esitarski/LaserJig/lasercut/lasercut.scad

UP = 0;
DOWN = 180;
LEFT = 90;
RIGHT = 270;
MID = 360;
kerf=0.0;// Hacky global for kerf

generate = 0; 

if (generate == 1)
{
    // openscad examples.scad -D generate=1 -o /tmp/d.csg 2>&1 >/dev/null  | sed 's/ECHO: \"\[LC\] //' | sed 's/"$//' | sed '$a;' >./generate.scad ; openscad ./generate.scad -o generate.dxf
    // (from http://forum.openscad.org/Sharing-Dump-echo-output-to-a-file-td12529.html)
//    echo("[LC] use <lasercut.scad>; \nprojection(cut = false) \n\t");
}


module lasercutoutSquare(thickness, x=0, y=0, 
        simple_tabs=[], simple_tab_holes=[], 
        captive_nuts=[], captive_nut_holes = [],
        finger_joints = [],
        bumpy_finger_joints = [],
        screw_tabs=[], screw_tab_holes=[],
        twist_holes=[], twist_connect=[],
        clips=[], clip_holes=[],
        circles_add = [],
        circles_remove = [],
        slits = [],
        cutouts = [],
        cutouts_vb = [],
        flat_adjust = [],
        milling_bit = 0.0,
)
{
    points = [[0,0], [x,0], [x,y], [0,y], [0,0]];
lasercutout(thickness=thickness,  
        points = points, 
        simple_tabs = simple_tabs, 
        simple_tab_holes = simple_tab_holes, 
        captive_nuts = captive_nuts, 
        captive_nut_holes = captive_nut_holes,
        finger_joints = finger_joints,
        bumpy_finger_joints = bumpy_finger_joints,
        screw_tabs= screw_tabs, screw_tab_holes= screw_tab_holes,
        twist_holes=twist_holes, twist_connect=twist_connect,
        clips=clips, clip_holes=clip_holes,
        circles_add = circles_add,
        circles_remove = circles_remove,
        slits = slits,
        cutouts = cutouts,
        cutouts_vb = cutouts_vb,
        flat_adjust = flat_adjust,
        milling_bit = milling_bit
    );
}

module lasercutout(thickness,  points= [], 
        simple_tabs=[], simple_tab_holes=[], 
        captive_nuts=[], captive_nut_holes = [],
        finger_joints = [],
        bumpy_finger_joints = [],
        screw_tabs=[], screw_tab_holes=[],
        twist_holes=[], twist_connect=[],
        clips=[], clip_holes=[],
        circles_add = [],
        circles_remove = [],
        slits = [],
        cutouts = [],
        cutouts_vb = [],
        flat_adjust = [],
        milling_bit = 0.0,
)
{
    function max_y(points) = max([for (a = [0:1:len(points)-1])  points[a][1]]);    
    function min_y(points) = min([for (a = [0:1:len(points)-1])  points[a][1]]);    
    function max_x(points) = max([for (a = [0:1:len(points)-1])  points[a][0]]);    
    function min_x(points) = min([for (a = [0:1:len(points)-1])  points[a][0]]);    
    
    max_y = max_y(points);
    min_y = min_y(points);
    max_x = max_x(points);
    min_x = min_x(points);
    
    difference() 
    { 
        union() 
        {
            linear_extrude(height = thickness , center = false)  polygon(points=points);
            if(simple_tabs != undef) for (t = [0:1:len(simple_tabs)-1]) 
            {
                simpleTab(simple_tabs[t][0], simple_tabs[t][1], simple_tabs[t][2], thickness);
            }
            if(captive_nuts != undef) for (t = [0:1:len(captive_nuts)-1]) 
            {
                captiveNutTab(captive_nuts[t][0], captive_nuts[t][1], captive_nuts[t][2], thickness);
            }    
            if(circles_add != undef) for (t = [0:1:len(circles_add)-1]) 
            {
                circlesAdd(circles_add[t][0], circles_add[t][1], circles_add[t][2], thickness);
            }    
            if(finger_joints != undef) for (t = [0:1:len(finger_joints)-1]) 
            {
                fingerJoint(finger_joints[t][0], finger_joints[t][1], finger_joints[t][2], thickness, max_y, min_y, max_x, min_x);
            }    
            if(bumpy_finger_joints != undef) for (t = [0:1:len(bumpy_finger_joints)-1]) 
            {
                fingerJoint(bumpy_finger_joints[t][0], bumpy_finger_joints[t][1], bumpy_finger_joints[t][2], thickness, max_y, min_y, max_x, min_x, bumps=true);
            }
            if(screw_tabs != undef) for (t = [0:1:len(screw_tabs)-1]) 
            {
                screwTab(screw_tabs[t][0], screw_tabs[t][1], screw_tabs[t][2], screw_tabs[t][3], thickness);
            }      
             if(clips != undef) for (t = [0:1:len(clips)-1]) 
            {
                clipTab(clips[t][0], clips[t][1], clips[t][2], thickness);
            }  
        } // end union

        if(simple_tab_holes != undef) for (t = [0:1:len(simple_tab_holes)-1]) 
        {
            simpleTabHole(simple_tab_holes[t][0], simple_tab_holes[t][1], simple_tab_holes[t][2], thickness);
        }
        if(captive_nuts != undef) for (t = [0:1:len(captive_nuts)-1]) 
        {
            if (len(captive_nuts) < 4) {
                captiveNutBoltHole(captive_nuts[t][0], captive_nuts[t][1], captive_nuts[t][2], thickness*3, thickness);
            } else {
                captiveNutBoltHole(captive_nuts[t][0], captive_nuts[t][1], captive_nuts[t][2], captive_nuts[t][3], thickness);
            }
        }
        if(captive_nut_holes != undef) for (t = [0:1:len(captive_nut_holes)-1]) 
        {
            captiveNutHole(captive_nut_holes[t][0], captive_nut_holes[t][1], captive_nut_holes[t][2], thickness);
        }    
        if(twist_holes != undef) for (t = [0:1:len(twist_holes)-1]) 
        {
            if(twist_holes[t][4] != undef) 
            {
                twistHole(twist_holes[t][0], twist_holes[t][1], twist_holes[t][2], twist_holes[t][3], thickness, spine=twist_holes[t][4]);
            }
            else
            {
                twistHole(twist_holes[t][0], twist_holes[t][1], twist_holes[t][2], twist_holes[t][3], thickness, spine=3*thickness);
            }
        }    
        if(twist_connect != undef) for (t = [0:1:len(twist_connect)-1]) 
        {
            if(twist_connect[t][3] != undef) 
            {
                twistConnect(twist_connect[t][0], twist_connect[t][1], twist_connect[t][2], thickness, max_y, min_y, max_x, min_x, spine=twist_connect[t][3]);
            }
            else
            {
                twistConnect(twist_connect[t][0], twist_connect[t][1], twist_connect[t][2], thickness, max_y, min_y, max_x, min_x, spine=thickness*3);
            }
        }    
        if(clips != undef) for (t = [0:1:len(clips)-1]) 
        {
            clipInner(clips[t][0], clips[t][1], clips[t][2], thickness);
        }    
        if(clip_holes != undef) for (t = [0:1:len(clip_holes)-1]) 
        {
            clipHole(clip_holes[t][0], clip_holes[t][1], clip_holes[t][2], thickness);
        }    
        if(circles_remove != undef) for (t = [0:1:len(circles_remove)-1]) 
        {
            circlesRemove(circles_remove[t][0], circles_remove[t][1], circles_remove[t][2], thickness);
        }    
        if(slits != undef) for (t = [0:1:len(slits)-1]) 
        {
               simpleSlit(slits[t][0], slits[t][1], slits[t][2], slits[t][3], thickness);
        }
        if(cutouts != undef) for (t = [0:1:len(cutouts)-1]) 
        {
               simpleCutouts(cutouts[t][0], cutouts[t][1], cutouts[t][2], cutouts[t][3], thickness);
        }
        if(cutouts_vb != undef) for (t = [0:1:len(cutouts_vb)-1]) 
        {
               simpleCutouts(cutouts_vb[t][0], cutouts_vb[t][1], cutouts_vb[t][2], cutouts_vb[t][3], thickness);
        }
        if(screw_tabs != undef) for (t = [0:1:len(screw_tabs)-1]) 
        {
               screwTabHoleForScrew(screw_tabs[t][0], screw_tabs[t][1], screw_tabs[t][2], screw_tabs[t][3], thickness);
        }
        if(screw_tab_holes != undef) for (t = [0:1:len(screw_tab_holes)-1]) 
        {
               screwTabHole(screw_tab_holes[t][0], screw_tab_holes[t][1], screw_tab_holes[t][2], screw_tab_holes[t][3], thickness);
        }
        // Used for milling (not lasercutting) fingerJoint, 
        if (milling_bit > 0.0)
        {
            for (t = [0:1:len(finger_joints)-1]) 
            {
                    fingerJoint(finger_joints[t][0], finger_joints[t][1], finger_joints[t][2], thickness, max_y, min_y, max_x, min_x, not_mill=false, milling_bit=milling_bit);
            } 
        }
    }
    
    if (flat_adjust)
    {
        if ($children) translate([0 + flat_adjust[0], max_y(points) + thickness*3 + milling_bit*2 + flat_adjust[1], 0])
                children();
    }
    else
    {
        if ((thickness*2.5 + milling_bit*2) > 5)
        {
            if ($children) translate([0, max_y(points) + thickness*2.5 + milling_bit*2, 0])
                    children();        
        }
        else
        {
            if ($children) translate([0, max_y(points) + 5, 0])
                    children();                
        }
    }

    if (generate == 1)
    {
        echo(str("[LC] lasercutout(thickness = ",thickness,", \n          points = ",points));
        if(simple_tabs)
            echo(str("[LC]         , simple_tabs = ", simple_tabs));
        if(simple_tab_holes)
            echo(str("[LC]         , simple_tab_holes = ", simple_tab_holes));
        if(captive_nuts)
            echo(str("[LC]         , captive_nuts = ", captive_nuts));
        if(captive_nut_holes)
            echo(str("[LC]         , captive_nut_holes = ", captive_nut_holes));
        if(finger_joints)
            echo(str("[LC]         , finger_joints = ", finger_joints));
        if(bumpy_finger_joints)
            echo(str("[LC]         , bumpy_finger_joints = ", bumpy_finger_joints));
        if(screw_tabs)
            echo(str("[LC]         , screw_tabs = ", screw_tabs));
        if(screw_tab_holes)
            echo(str("[LC]         , screw_tab_holes = ", screw_tab_holes));
        if(twist_holes)
            echo(str("[LC]         , twist_holes = ", twist_holes));
        if(twist_connect)
            echo(str("[LC]         , twist_connect = ", twist_connect));
        if(clips)
            echo(str("[LC]         , clips = ", clips));
        if(clip_holes)
            echo(str("[LC]         , clip_holes = ", clip_holes));
        if(circles_add)
            echo(str("[LC]         , circles_add = ", circles_add));
        if(circles_remove)
            echo(str("[LC]         , circles_remove = ", circles_remove));
        if(slits)
            echo(str("[LC]         , slits = ", slits));
        if(cutouts)
            echo(str("[LC]         , cutouts = ", cutouts));
        if(cutouts_vb)
            echo(str("[LC]         , cutouts_vb = ", cutouts_vb));
        if(flat_adjust)
            echo(str("[LC]         , flat_adjust = ", flat_adjust));
        if(milling_bit>0)
            echo(str("[LC]         , milling_bit = ", milling_bit));
        echo("[LC]         ) \n");
    }
}



module simpleTab(angle, x, y, thickness)
{
    translate([x,y,0]) rotate([0,0,angle]) translate([-thickness/2,0,0]) cube([thickness, thickness, thickness]); 
}

module simpleTabHole(angle, x, y, thickness)
{
     // Special case does not go past edge - so make only 1 thickness y
     if (angle == 360)
     {
         translate([x,y,0]) rotate([0,0,0]) translate([0,0,-thickness]) cube([thickness, thickness, thickness*3]); 
     }
     else
     {
         translate([x,y,0]) rotate([0,0,angle-180]) translate([-thickness/2,-thickness,-thickness]) cube([thickness, thickness, thickness*3]); 
     }
}

module captiveNutBoltHole(angle, x, y, nut_flat_width, thickness)
{
    translate([x,y,0]) rotate([0,0,angle-180]) union() 
    {
        translate([-thickness/2,-thickness,-thickness]) cube([thickness, thickness*4, thickness*3]); 
        echo(str("[LC] // screw thread major dia must be < ", thickness));
        echo(str("[LC] // screw thread length must be < ", thickness*5));
        translate([-nut_flat_width/2,thickness,-thickness]) cube([nut_flat_width, thickness, thickness*3]); 
        echo(str("[LC] // nut thickness must be < ", thickness));
        echo(str("[LC] // nut flats must be < ", nut_flat_width));
    }
}

module fingerJoint(angle, start_up, fingers, thickness, max_y, min_y, max_x, min_x, bumps = false, not_mill=true, milling_bit=0)
{
    if ( angle == UP )
    {
        range_min = min_x; 
        range_max = max_x; 
        t_x = min_x;
        t_y = max_y;
        if(not_mill)
        {
            fingers(angle, start_up, fingers, thickness, range_min, range_max, t_x, t_y, bumps = bumps);
        }
        else
        {
            fingers_mill(angle, start_up, fingers, thickness, range_min, range_max, t_x, t_y, bit=milling_bit);
        }
    }
    if ( angle == DOWN )
    {
        range_min = min_x; 
        range_max = max_x; 
        t_x = max_x;
        t_y = min_y;
        if(not_mill)
        {
            fingers(angle, start_up, fingers, thickness, range_min, range_max, t_x, t_y, bumps = bumps);
        }
        else
        {
            fingers_mill(angle, start_up, fingers, thickness, range_min, range_max, t_x, t_y, bit=milling_bit);
        }
    }
    if ( angle == LEFT )
    {
        range_min = min_y; 
        range_max = max_y; 
        t_x = min_x;
        t_y = min_y;
        if(not_mill)
        {
            fingers(angle, start_up, fingers, thickness, range_min, range_max, t_x, t_y, bumps = bumps);
        }
        else
        {
            fingers_mill(angle, start_up, fingers, thickness, range_min, range_max, t_x, t_y, bit=milling_bit);
        }
    }
    if ( angle == RIGHT )
    {
        range_min = min_y; 
        range_max = max_y; 
        t_x = max_x;
        t_y = max_y;
        if(not_mill)
        {
            fingers(angle, start_up, fingers, thickness, range_min, range_max, t_x, t_y, bumps = bumps);
        }
        else
        {
            fingers_mill(angle, start_up, fingers, thickness, range_min, range_max, t_x, t_y, bit=milling_bit);
        }
    }

}


module fingers(angle, start_up, fingers, thickness, range_min, range_max, t_x, t_y, bumps = false)
{

    // The tweaks to y translate([0, -thickness,0]) ... thickness*2 rather than *1
    // Are to avoid edge cases and make the dxf export better.
    // All fun
    translate([t_x, t_y,0]) rotate([0,0,angle]) translate([0, -thickness,0])
    {
        for ( p = [ 0 : 1 : fingers-1] )
		{
		
			kerfSize = (p > 0) ? kerf/2 : kerf/2 ;
			kerfMove = (p > 0) ? kerf/4 : 0;
			
			i=range_min + ((range_max-range_min)/fingers)*p;
            if(start_up == 1) 
            {
			
                translate([i-kerfMove,0,0]) 
                {
                    cube([ (range_max-range_min)/(fingers*2) + kerfSize, thickness*2, thickness]);
                    if(bumps == true)
                    {
                        translate([(range_max-range_min)/(fingers*2), thickness*1.5, 0]) cylinder(h=thickness, r=thickness/10);
                    }
                }
            }
            else 
            {
                translate([i+(range_max-range_min)/(fingers*2)-kerfMove,0,0]) 
                {
                    cube([ (range_max-range_min)/(fingers*2)+kerfSize, thickness*2, thickness]);
                    if(bumps == true)
                    {
                        if (i < (range_max - (range_max-range_min)/fingers ))
                        {
                            translate([(range_max-range_min)/(fingers*2), thickness*1.5, 0]) cylinder(h=thickness, r=thickness/10);
                        }
                    }
                }
            }
        }
    }

}

module fingers_mill(angle, start_up, fingers, thickness, range_min, range_max, t_x, t_y, bit=6.35/2)
{

    // The tweaks to y translate([0, -thickness,0]) ... thickness*2 rather than *1
    // Are to avoid edge cases and make the dxf export better.
    // All fun
    translate([t_x, t_y,0]) rotate([0,0,angle]) translate([0, -thickness,0])
    {
        for ( p = [ 0 : 1 : fingers-1] )
		{
            if(start_up == 1) 
            {
                translate([((range_max-range_min)/fingers)*p,0,0]) 
                {
                    translate([(range_max-range_min)/(fingers*2) + bit/2,thickness,0]) cylinder(h=thickness*4, d=bit, center=true );
                    translate([2*(range_max-range_min)/(fingers*2) - bit/2,thickness,0]) cylinder(h=thickness*4, d=bit, center=true );
                }
            }
            else 
            {
                translate([((range_max-range_min)/fingers)*p,0,0]) 
                {
                    translate([bit/2,thickness,0]) cylinder(h=thickness*4, d=bit, center=true );
                    translate([(range_max-range_min)/(fingers*2) - bit/2,thickness,0]) cylinder(h=thickness*4, d=bit, center=true );
                }
            }
        }
    }

}



module screwTab(angle, x, y, screw, thickness)
{
    translate([x,y,0]) rotate([0,0,angle]) translate([-screw/2,0,0]) cube([screw*2, thickness+screw*2, thickness]); 
}

module screwTabHoleForScrew(angle, x, y, screw, thickness)
{
    // not to be confused with screwTabHole
    translate([x,y,0]) rotate([0,0,angle]) translate([screw/2,thickness+screw,-thickness]) cylinder(h=thickness*3, r=screw/2); 
}

module screwTabHole(angle, x, y, screw, thickness)
{
     // Special case does not go past edge - so make only 1 thickness y
     if (angle == 360)
     {
         translate([x,y,0]) rotate([0,0,0]) translate([0,0,-thickness]) cube([screw*2, thickness, thickness*3]); 
     }
     else
     {
         translate([x,y,0]) rotate([0,0,angle-180]) translate([-thickness/2,-thickness,-thickness]) cube([thickness, thickness*2, thickness*3]); 
     }
}


module captiveNutTab(angle, x, y, thickness)
{
    translate([x,y,0]) rotate([0,0,angle]) union()
    {
        translate([-thickness/2+thickness*2,-thickness,0]) cube([thickness*3, thickness*2, thickness]); 
        translate([-thickness/2-thickness*4,-thickness,0]) cube([thickness*3, thickness*2, thickness]); 
    }
}

module captiveNutHole(angle, x, y, thickness)
{
    translate([x,y,0]) rotate([0,0,angle]) union()
    {
        translate([-thickness/2,-thickness*2,-thickness]) cube([thickness, thickness, thickness*3]); 
        translate([-thickness/2+thickness*2,-thickness*2,-thickness]) cube([thickness*3, thickness, thickness*3]); 
        translate([-thickness/2-thickness*4,-thickness*2,-thickness]) cube([thickness*3, thickness, thickness*3]); 
    }
}

module twistHole(angle, x, y, width, thickness, spine)
{
// http://msraynsford.blogspot.co.uk/2012/06/panel-joinery-10.html
    translate([x,y,0]) rotate([0,0,angle-90]) union()
    {
        cube([width, thickness, thickness*3], center=true); 
        difference()
        {
            // Need some trig,  radius is hypo of triangle
            // Other sides are thinkness/2 and spine
            // 
            // 
           radius = sqrt(  ((thickness/2)*(thickness/2)) + ((spine/2)*(spine/2)) ); 
           translate([0,0, -thickness]) cylinder(h=thickness*3, r=radius);
           translate([-thickness/2-spine/4,spine/4,0]) cube([(spine/2), (spine/2), thickness*3], center=true); 
           translate([+thickness/2+spine/4,-spine/4,0]) cube([(spine/2), (spine/2), thickness*3], center=true); 
        }
    }
}

module twistConnect(angle, x, y, thickness, max_y, min_y, max_x, min_x, spine)
{
    // Really should do trianometry for non-90 Angles, but hey ho
    if( (angle == LEFT) || (angle == RIGHT) )
    {
        translate([0,y,-thickness]) rotate([0,0,angle+90]) union()
        {
            gap = max_x - min_x;
            translate([-gap/2-(spine/2),0,0]) cube([gap, thickness, thickness*3]); 
            translate([+gap/2+(spine/2),0,0]) cube([gap, thickness, thickness*3]); 
        }
    }
    if( (angle == UP) || (angle == DOWN) )
    {
        translate([x,0,-thickness]) rotate([0,0,angle+90]) union()
        {
            gap = max_y - min_y;
            translate([-gap/2-(spine/2),0,0]) cube([gap, thickness, thickness*3]); 
            translate([+gap/2+(spine/2),0,0]) cube([gap, thickness, thickness*3]); 
        }
    }
}

module clipInner(angle, x, y, thickness)
{
    translate([x,y,0]) rotate([0,0,angle]) union()
    {
        translate([-thickness/2-1,0,0])
        {
            translate([-(1+thickness)/2,-thickness*10,-thickness]) cube([1, thickness*11, thickness*3]);
            translate([(1+thickness)/2+1,-thickness*8,0])  linear_extrude(height = thickness*3, center = true)  polygon(points=[[0,0],[0,9*thickness],[-(thickness-1), 9*thickness]]);
            translate([(1+thickness)/2+1-thickness+1,thickness-1,-thickness]) cube([thickness/2, thickness, thickness*3]);
            translate([-thickness*3/2,0,-thickness]) cube([thickness, thickness, thickness*3]);
        }
    }
}

module clipTab(angle, x, y, thickness)
{
    translate([x,y,0]) rotate([0,0,angle]) union()
    {
        // make off-center
        translate([-thickness/2-1,0,0])
        {
            difference()
            {
                 translate([0,thickness/2,thickness/2]) cube([thickness+1,thickness,thickness], center=true);
                 translate([(1+thickness)/2+1,-thickness*8,0])  linear_extrude(height = thickness*3, center = true)  polygon(points=[[0,0],[0,9*thickness],[-(thickness-1), 9*thickness]]);
            }
           translate([-thickness,thickness,0])  linear_extrude(height = thickness)  polygon(points=[[0,0],[thickness+1,0],[thickness,thickness-1],[1,thickness-1]]);
        }
        translate([0.5,0,0]) cube([thickness,thickness,thickness]);
*       cube([thickness*2+1,thickness,thickness], center=true);       
    }
}

module clipHole(angle, x, y, thickness)
{
    translate([x,y,0]) rotate([0,0,angle]) union()
    {
        translate([0,-thickness/2,thickness/2]) cube([thickness*2+1,thickness,thickness*3], center=true);
    }
}

module circlesAdd(radius, x, y, thickness)
{
    translate([x,y,0]) cylinder(h=thickness, r=radius);
}

module circlesRemove(radius, x, y, thickness)
{
    translate([x,y,-thickness]) cylinder(h=thickness*3, r=radius);
}


module simpleSlit(angle, x, y, length, thickness)
{
     translate([x,y,0]) rotate([0,0,angle-180]) translate([-thickness/2,-thickness,-thickness]) cube([thickness, length+thickness, thickness*3]);
}

module simpleCutouts(x, y, width, height, thickness)
{
    translate([x,y,0]) rotate([0,0,0]) translate([0,0,-thickness]) cube([width, height, thickness*3]);
}

module lasercutoutBox(thickness, x=0, y=0, z=0, sides=6, num_fingers=2,
        simple_tab_holes_a=[], 
        captive_nuts_a=[], captive_nut_holes_a=[],
        screw_tab_holes_a=[],
        twist_holes_a=[],
        clip_holes_a=[],
        circles_add_a=[],
        circles_remove_a=[],
        slits_a = [],
        cutouts_a = [],
        milling_bit = 0.0
)
{

    if (sides==4)
    {
        fj = [
            [ [UP, 1, num_fingers], [DOWN, 1, num_fingers],    ],
            [ [UP, 0, num_fingers], [DOWN, 1, num_fingers],    ],
            [ [UP, 1, num_fingers], [DOWN, 0, num_fingers],    ],
            [ [UP, 1, num_fingers], [DOWN, 1, num_fingers],    ],
        ];
        translate([0,thickness,0]) lasercutoutBoxAdjustedFJ(thickness = thickness, x=x, y=y-thickness*2 , z=z-thickness*2, sides=sides, fj=fj,
            simple_tab_holes_a=simple_tab_holes_a, 
            captive_nuts_a=captive_nuts_a, captive_nut_holes_a=captive_nut_holes_a,
            screw_tab_holes_a=screw_tab_holes_a,
            twist_holes_a=twist_holes_a,
            clip_holes_a=clip_holes_a,
            circles_add_a=circles_add_a,
            circles_remove_a=circles_remove_a,
            slits_a=slits_a,
            cutouts_a=cutouts_a,
            milling_bit = milling_bit
        );
    }
    if (sides==5)
    {
        st = [
        [[DOWN, -thickness/2, 0], [DOWN, -thickness/2, y-thickness] ],
        [[DOWN, -thickness/2, 0], ],
        [[UP, -thickness/2, z-thickness*2], ],
        ];
        fj = [
            [ [UP, 1, num_fingers], [DOWN, 1, num_fingers], [LEFT, 1, num_fingers],   ],
            [ [UP, 0, num_fingers], [DOWN, 1, num_fingers], [LEFT, 1, num_fingers],   ],
            [ [UP, 1, num_fingers], [DOWN, 0, num_fingers], [LEFT, 1, num_fingers],   ],
            [ [UP, 1, num_fingers], [DOWN, 1, num_fingers], [LEFT, 1, num_fingers],   ],
            [ [UP, 0, num_fingers], [DOWN, 1, num_fingers], [LEFT, 0, num_fingers], [RIGHT, 1, num_fingers]  ],
        ];
        
        translate([thickness,thickness,0]) lasercutoutBoxAdjustedFJ(thickness = thickness, x=x-thickness, y=y-thickness*2 , z=z-thickness*2, sides=sides, fj=fj, st=st,
            simple_tab_holes_a=simple_tab_holes_a, 
            captive_nuts_a=captive_nuts_a, captive_nut_holes_a=captive_nut_holes_a,
            screw_tab_holes_a=screw_tab_holes_a,
            twist_holes_a=twist_holes_a,
            clip_holes_a=clip_holes_a,
            circles_add_a=circles_add_a,
            circles_remove_a=circles_remove_a,
            slits_a=slits_a,
            cutouts_a=cutouts_a,
            milling_bit = milling_bit
        );

        }
    if (sides==6)
    {
        st = [
        [[DOWN, -thickness/2, 0], [DOWN, -thickness/2, y-thickness] , [RIGHT, x-thickness*2, -thickness/2]],
        [[DOWN, -thickness/2, 0], [RIGHT, x-thickness*2, -thickness/2]],
        [[UP, -thickness/2, z-thickness*2], [DOWN, x-thickness*1.5, 0], ],
        [[UP, z-thickness*1.5, y-thickness*2], ],
        ];
        fj = [
            [ [UP, 1, num_fingers], [DOWN, 1, num_fingers], [LEFT, 1, num_fingers], [RIGHT, 0, num_fingers]  ],
            [ [UP, 0, num_fingers], [DOWN, 1, num_fingers], [LEFT, 1, num_fingers], [RIGHT, 0, num_fingers]  ],
            [ [UP, 1, num_fingers], [DOWN, 0, num_fingers], [LEFT, 1, num_fingers], [RIGHT, 0, num_fingers]  ],
            [ [UP, 1, num_fingers], [DOWN, 1, num_fingers], [LEFT, 1, num_fingers], [RIGHT, 0, num_fingers]  ],
            [ [UP, 0, num_fingers], [DOWN, 1, num_fingers], [LEFT, 0, num_fingers], [RIGHT, 1, num_fingers]  ],
            [ [UP, 0, num_fingers], [DOWN, 1, num_fingers], [LEFT, 0, num_fingers], [RIGHT, 1, num_fingers]  ],
        ];
        translate([thickness,thickness,0]) lasercutoutBoxAdjustedFJ(thickness = thickness, x=x-thickness*2, y=y-thickness*2 , z=z-thickness*2, sides=sides, fj=fj, st=st,
            simple_tab_holes_a=simple_tab_holes_a, 
            captive_nuts_a=captive_nuts_a, captive_nut_holes_a=captive_nut_holes_a,
            screw_tab_holes_a=screw_tab_holes_a,
            twist_holes_a=twist_holes_a,
            clip_holes_a=clip_holes_a,
            circles_add_a=circles_add_a,
            circles_remove_a=circles_remove_a,
            slits_a=slits_a,
            cutouts_a=cutouts_a,
            milling_bit = milling_bit
        );

    }    
}


module lasercutoutBoxAdjustedFJ(thickness, x=0, y=0, z=0, sides=6, fj=[], st=[],
        simple_tab_holes_a=[], 
        captive_nuts_a=[], captive_nut_holes_a = [],
        screw_tab_holes_a = [],
        twist_holes_a = [],
        clip_holes_a = [],
        circles_add_a = [],
        circles_remove_a = [],
        slits_a = [],
        cutouts_a = [],
        milling_bit = 0.0
)
{

    translate([0,0,0]) lasercutoutSquare(thickness=thickness,x=x, y=y, simple_tabs = st[0], finger_joints = fj[0],
                                simple_tab_holes=simple_tab_holes_a[0], captive_nuts=captive_nuts_a[0],
                                captive_nut_holes = captive_nut_holes_a[0],
                                screw_tab_holes = screw_tab_holes_a[0],
                                twist_holes = twist_holes_a[0],
                                clip_holes = clip_holes_a[0],
                                circles_add = circles_add_a[0], circles_remove = circles_remove_a[0],
                                slits = slits_a[0],
                                cutouts = cutouts_a[0],
                                milling_bit = milling_bit);

    translate([0,0,z+thickness]) lasercutoutSquare(thickness=thickness,x=x, y=y, simple_tabs = st[1], finger_joints = fj[1],
                                simple_tab_holes=simple_tab_holes_a[1], captive_nuts=captive_nuts_a[1],
                                captive_nut_holes = captive_nut_holes_a[1],
                                screw_tab_holes = screw_tab_holes_a[1],
                                twist_holes = twist_holes_a[1],
                                clip_holes = clip_holes_a[1],
                                circles_add = circles_add_a[1], circles_remove = circles_remove_a[1],
                                slits = slits_a[1],
                                cutouts = cutouts_a[1],
                                milling_bit = milling_bit);

    translate([0,0,thickness]) rotate([90,0,0]) lasercutoutSquare(thickness=thickness,x=x, y=z, finger_joints = fj[2],
                                simple_tab_holes=simple_tab_holes_a[2], captive_nuts=captive_nuts_a[2],
                                captive_nut_holes = captive_nut_holes_a[2],
                                screw_tab_holes = screw_tab_holes_a[2],
                                twist_holes = twist_holes_a[2],
                                clip_holes = clip_holes_a[2],
                                circles_add = circles_add_a[2], circles_remove = circles_remove_a[2],
                                slits = slits_a[2],
                                cutouts = cutouts_a[2],
                                milling_bit = milling_bit);

    translate([0,y+thickness,thickness]) rotate([90,0,0]) lasercutoutSquare(thickness=thickness,x=x, y=z, simple_tabs = st[2], 
                                finger_joints = fj[3],
                                simple_tab_holes=simple_tab_holes_a[3], captive_nuts=captive_nuts_a[3],
                                captive_nut_holes = captive_nut_holes_a[3],
                                screw_tab_holes = screw_tab_holes_a[3],
                                twist_holes = twist_holes_a[3],
                                clip_holes = clip_holes_a[3],
                                circles_add = circles_add_a[3], circles_remove = circles_remove_a[3],
                                slits = slits_a[3],
                                cutouts = cutouts_a[3],
                                milling_bit = milling_bit
                                );
    
    if (sides>4)
    {
        translate([0,0,thickness]) rotate([0,-90,0]) lasercutoutSquare(thickness=thickness,x=z, y=y, finger_joints = fj[4],
                                simple_tab_holes=simple_tab_holes_a[4], captive_nuts=captive_nuts_a[4],
                                captive_nut_holes = captive_nut_holes_a[4],
                                screw_tab_holes = screw_tab_holes_a[4],
                                twist_holes = twist_holes_a[4],
                                clip_holes = clip_holes_a[4],
                                circles_add = circles_add_a[4], circles_remove = circles_remove_a[4],
                                slits = slits_a[4],
                                cutouts = cutouts_a[4],
                                milling_bit = milling_bit);
        }
    
    if (sides>5)
    {
        translate([x+thickness,0,thickness]) rotate([0,-90,0]) lasercutoutSquare(thickness=thickness,x=z, y=y, 
                                simple_tabs = st[3], finger_joints = fj[5],
                                simple_tab_holes=simple_tab_holes_a[5], captive_nuts=captive_nuts_a[5],
                                captive_nut_holes = captive_nut_holes_a[5],
                                screw_tab_holes = screw_tab_holes_a[5],
                                twist_holes = twist_holes_a[5],
                                clip_holes = clip_holes_a[5],
                                circles_add = circles_add_a[5], circles_remove = circles_remove_a[5],
                                slits = slits_a[5],
                                cutouts = cutouts_a[5],
                                milling_bit = milling_bit);
    }
}

module lasercutoutVinylBox(thickness, x=0, y=0, z=0, sides=6, overlapdistance=-1,
        infill=false,
        infill_x=5,
        infill_y=5,
        simple_tab_holes_a=[], 
        captive_nuts_a=[], captive_nut_holes_a=[],
        screw_tab_holes_a=[],
        twist_holes_a=[],
        clip_holes_a=[],
        circles_add_a=[],
        circles_remove_a=[],
        slits_a = [],
        cutouts_a = [],
        milling_bit = 0.0
)
{
    overlap = (overlapdistance == -1) ? (1+10)*thickness : overlapdistance;

    gap_y = (x-(overlap+thickness)-(overlap+thickness))/infill_x;
    gap_x = (y-(overlap+thickness)-(overlap+thickness))/infill_y;

    cutouts_y = [for(i = [(overlap+thickness): gap_x : y-(overlap+thickness)-(overlap+thickness)]) [z/2, i+gap_x/2, z/2, thickness] ];
    cutouts_x = [for(i = [(overlap+thickness): gap_y : x-(overlap+thickness)-(overlap+thickness)]) [i+gap_y/2, 0, thickness, z/2] ];
    cutouts_x_extend = [for(i = [(overlap+thickness): gap_y : x-(overlap+thickness)-(overlap+thickness)]) [i+gap_y/2, z/3, thickness, z/3] ];
    cutouts_y_extend = [for(i = [(overlap+thickness): gap_x : y-(overlap+thickness)-(overlap+thickness)]) [z/3, i+gap_x/2, z/3, thickness] ];

    // cutout just for down protruding infill 
    cutouts_1 = [for(i = [(overlap+thickness): gap_x : y-(overlap+thickness)-(overlap+thickness)]) [x/3, i+gap_x/2, x/3, thickness] ];
    cutouts_2 = [for(i = [(overlap+thickness): gap_y : x-(overlap+thickness)-(overlap+thickness)]) [i+gap_y/2, y/3, thickness, y/3] ];

    cutouts_1_all = (infill) ? cutouts_1 : undef ;
    cutouts_2_all = (infill) ? cutouts_2 : undef ;

    cutouts_3_4 = [ 
            [x*1/3, overlap, x/3, thickness],
            [x*1/3, z-overlap-thickness, x/3, thickness],
            [overlap, z/3, thickness, z/3],
            [x-overlap-thickness, z/3, thickness, z/3]   
        ];
    
    
    cutout_3_4_all = (infill) ? concat(cutouts_3_4, cutouts_x_extend) : cutouts_3_4 ;
 
    cutouts_5_6= [ 
            [overlap, y/3, thickness, y/3],
            [z-overlap-thickness*2, y/3, thickness, y/3]
        ];

    cutout_5_6_all = (infill) ? concat(cutouts_5_6, cutouts_y_extend) : cutouts_5_6 ;

    points_1_2 = [
         [overlap+thickness,overlap+thickness], 
         [overlap+thickness,y*1/3], 
         [0,y*1/3], [0,y*2/3],
         [overlap+thickness,y*2/3], 
         [overlap+thickness,y-overlap-thickness], 
         [x*1/3,y-overlap-thickness], 
         [x*1/3,y], 
         [x*2/3,y], 
         [x*2/3,y-overlap-thickness], 
         [x-overlap-thickness,y-overlap-thickness], 
         [x-overlap-thickness,y*2/3], 
         [x,y*2/3], 
         [x,y*1/3], 
         [x-overlap-thickness,y*1/3], 
         [x-overlap-thickness,overlap+thickness], 
         [x*2/3,overlap+thickness], 
         [x*2/3,0], 
         [x*1/3,0], 
         [x*1/3,overlap+thickness],     
         ];

    points_5_6 = [
        [0,overlap+thickness], 
        [z/3,overlap+thickness], 
        [z/3,0], 
        [z*2/3,0], 
        [z*2/3,overlap+thickness], 
        [z*3/3,overlap+thickness], 
        [z*3/3,y-(overlap+thickness)], 
        [z*2/3,y-(overlap+thickness)], 
        [z*2/3,y], 
        [z*1/3,y], 
        [z*1/3,y-(overlap+thickness)], 
        [0,y-(overlap+thickness)]
        ];

    points_infil_x = [
        [overlap+thickness,overlap+thickness],
        [z/3,overlap+thickness],
        [z/3,0], [z*2/3,0],
        [z*2/3,overlap+thickness],
        [z-(overlap+thickness),overlap+thickness],
        [z-(overlap+thickness),y-(overlap+thickness)],
        [z*2/3,y-(overlap+thickness)],
        [z*2/3,y],
        [z*1/3,y],
        [z*1/3,y-(overlap+thickness)],
        [overlap+thickness,y-(overlap+thickness)],
        [overlap+thickness,y*2/3],
        [0,y*2/3],
        [0,y*1/3],
        [overlap+thickness,y*1/3],
        [overlap+thickness,overlap+thickness],
        ];

    points_infil_y = [
        [overlap+thickness,overlap+thickness],
        [overlap+thickness,z/3],
        [0,z/3],
        [0,z*2/3],
        [overlap+thickness,z*2/3],
        [overlap+thickness,z-(overlap+thickness)],
        [x/3,z-(overlap+thickness)],
        [x/3,z],
        [x*2/3,z],
        [x*2/3,z-(overlap+thickness)],
        [x-(overlap+thickness),z-(overlap+thickness)],
        [x-(overlap+thickness),z*2/3],
        [x,z*2/3],
        [x,z*1/3],
        [x-(overlap+thickness),z*1/3],
        [x-(overlap+thickness),(overlap+thickness)],
        [overlap+thickness,overlap+thickness],
        ];

   if (sides>0)
   {
        // side 1
        translate([0,0,overlap]) rotate([0,0,0]) lasercutout(thickness=thickness,
                points=points_1_2,
                cutouts_vb=cutouts_1_all,
                simple_tab_holes=simple_tab_holes_a[0], captive_nuts=captive_nuts_a[0],
                captive_nut_holes = captive_nut_holes_a[0],
                screw_tab_holes = screw_tab_holes_a[0],
                twist_holes = twist_holes_a[0],
                clip_holes = clip_holes_a[0],
                circles_add = circles_add_a[0], circles_remove = circles_remove_a[0],
                slits = slits_a[0],
                cutouts = cutouts_a[0],
                milling_bit = milling_bit
                );    
    }
   if (sides>1)
   {
        // side 2
        translate([x,0,z-overlap]) rotate([0,180,0]) lasercutout(thickness=thickness,
                points=points_1_2,
                cutouts_vb=cutouts_2_all,
                simple_tab_holes=simple_tab_holes_a[1], captive_nuts=captive_nuts_a[1],
                captive_nut_holes = captive_nut_holes_a[1],
                screw_tab_holes = screw_tab_holes_a[1],
                twist_holes = twist_holes_a[1],
                clip_holes = clip_holes_a[1],
                circles_add = circles_add_a[1], circles_remove = circles_remove_a[1],
                slits = slits_a[1],
                cutouts = cutouts_a[1],
                milling_bit = milling_bit
                );    
    }
    if (sides>2)
    {
        // side 3
        translate([0,overlap,z]) rotate([270,0,0])  lasercutoutSquare(thickness=thickness,
                x=x, y=z,
                cutouts_vb=cutout_3_4_all,
                simple_tab_holes=simple_tab_holes_a[2], captive_nuts=captive_nuts_a[2],
                captive_nut_holes = captive_nut_holes_a[2],
                screw_tab_holes = screw_tab_holes_a[2],
                twist_holes = twist_holes_a[2],
                clip_holes = clip_holes_a[2],
                circles_add = circles_add_a[2], circles_remove = circles_remove_a[2],
                slits = slits_a[2],
                cutouts = cutouts_a[2],
                milling_bit = milling_bit
                );        
    }
    if (sides>3)
    {
        // side 4
        translate([0,y-thickness-overlap,z]) rotate([270,0,0])  lasercutoutSquare(thickness=thickness,
                x=x, y=z,
                cutouts_vb=cutout_3_4_all,
                simple_tab_holes=simple_tab_holes_a[3], captive_nuts=captive_nuts_a[3],
                captive_nut_holes = captive_nut_holes_a[3],
                screw_tab_holes = screw_tab_holes_a[3],
                twist_holes = twist_holes_a[3],
                clip_holes = clip_holes_a[3],
                circles_add = circles_add_a[3], circles_remove = circles_remove_a[3],
                slits = slits_a[3],
                cutouts = cutouts_a[3],
                milling_bit = milling_bit
                );        
    }
    if (sides>4)
    {
        // Side 5
        translate([overlap,0,z]) rotate([0,90,0])  lasercutout(thickness=thickness,
                points=points_5_6,
                cutouts_vb=cutout_5_6_all,
                simple_tab_holes=simple_tab_holes_a[4], captive_nuts=captive_nuts_a[4],
                captive_nut_holes = captive_nut_holes_a[4],
                screw_tab_holes = screw_tab_holes_a[4],
                twist_holes = twist_holes_a[4],
                clip_holes = clip_holes_a[4],
                circles_add = circles_add_a[4], circles_remove = circles_remove_a[4],
                slits = slits_a[4],
                cutouts = cutouts_a[4],
                milling_bit = milling_bit
                );    
    }
    if (sides>5)
    {
        // Side 6
        translate([x-overlap,0,0]) rotate([0,270,0])  lasercutout(thickness=thickness,
                points=points_5_6,
                cutouts_vb=cutout_5_6_all,
                simple_tab_holes=simple_tab_holes_a[5], captive_nuts=captive_nuts_a[5],
                captive_nut_holes = captive_nut_holes_a[5],
                screw_tab_holes = screw_tab_holes_a[5],
                twist_holes = twist_holes_a[5],
                clip_holes = clip_holes_a[5],
                circles_add = circles_add_a[5], circles_remove = circles_remove_a[5],
                slits = slits_a[5],
                cutouts = cutouts_a[5],
                milling_bit = milling_bit
                );    
   }
   if (infill)
   {
        for(i = [(overlap+thickness): gap_y : x-(overlap+thickness)-(overlap+thickness)]) 
        {
            translate([i+gap_y/2,0,z]) rotate([0,90,0]) lasercutout(thickness=thickness,
                points=points_infil_x,
                cutouts=cutouts_y
                );
        }
        for(i = [(overlap+thickness): gap_x : y-(overlap+thickness)-(overlap+thickness)]) 
        {
            translate([0,i+gap_x/2,z]) rotate([270,0,0])   lasercutout(thickness=thickness,
                points=points_infil_y,
                cutouts=cutouts_x
                );
        }
   }
}
